Rian-Rasch/Projeto-I.-Eng.-El-trica---2024.1/Imagens Guia/Bateria Lítio.png

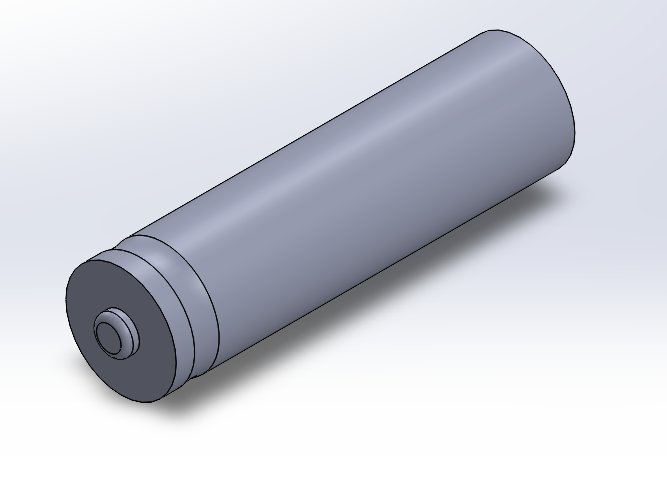
Imagens Guia/Bateria Lítio.png
