Rian-Rasch/Projeto-I.-Eng.-El-trica---2024.1/Imagens Guia/download.jpg

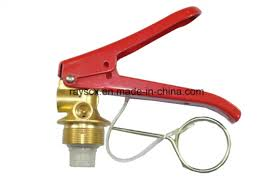
Imagens Guia/download.jpg
