Rian-Rasch/Projeto-I.-Eng.-El-trica---2024.1/Imagens Guia/EXTINTOR.png

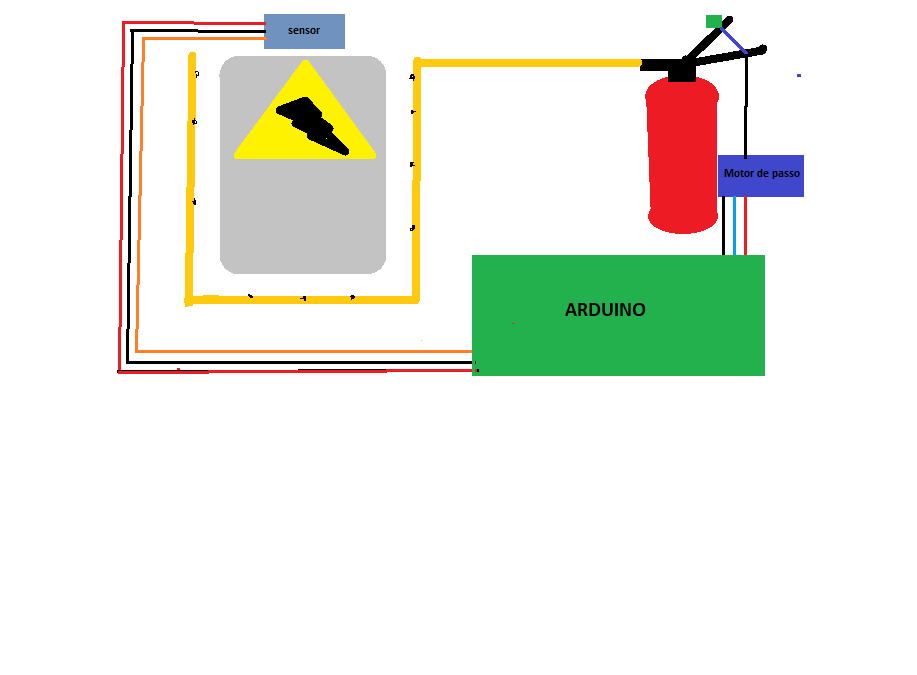
Imagens Guia/EXTINTOR.png
