Rian-Rasch/Projeto-I.-Eng.-El-trica---2024.1/Imagens Guia/S8efe8c3fdea14018a6a882b7f9c04156H.webp

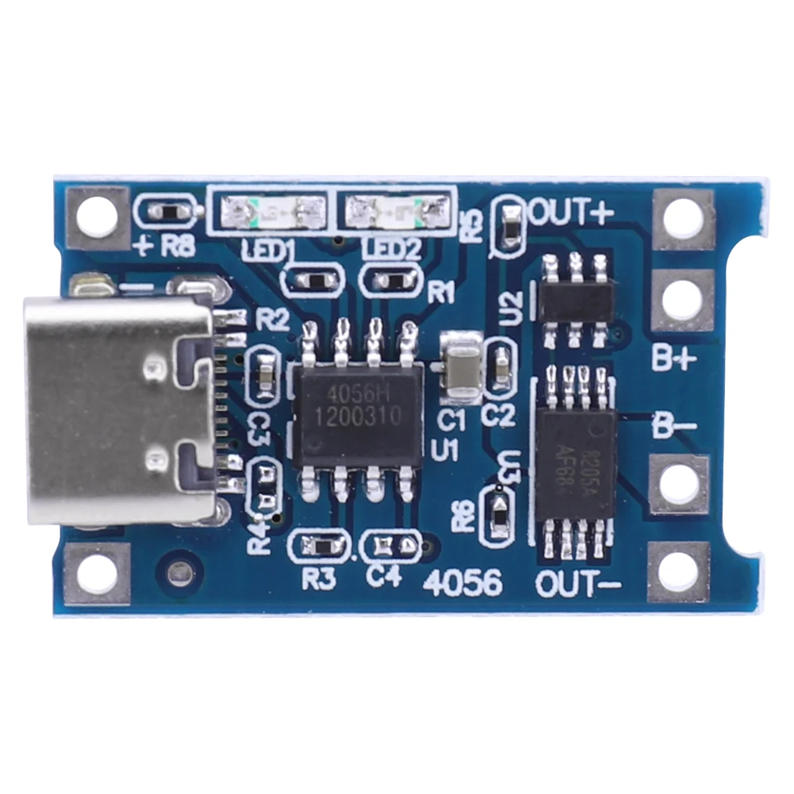
Imagens Guia/S8efe8c3fdea14018a6a882b7f9c04156H.webp
