Rian-Rasch/Projeto-I.-Eng.-El-trica---2024.1/Imagens Guia/Servomotor.png

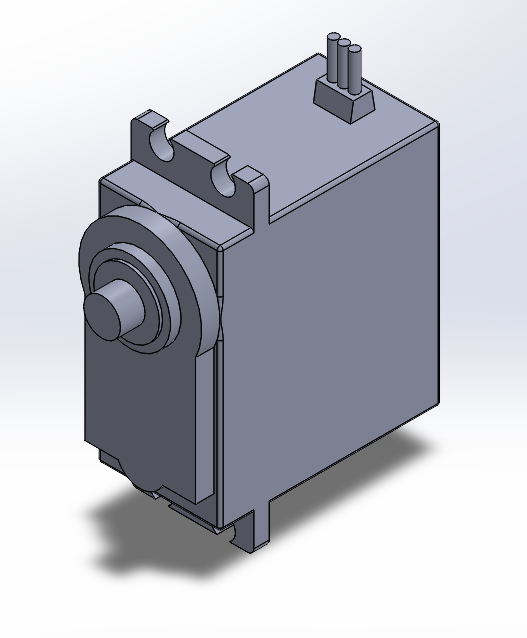
Imagens Guia/Servomotor.png
