Rian-Rasch/Projeto-I.-Eng.-El-trica---2024.1/Imagens Guia/Suporte Servo.png

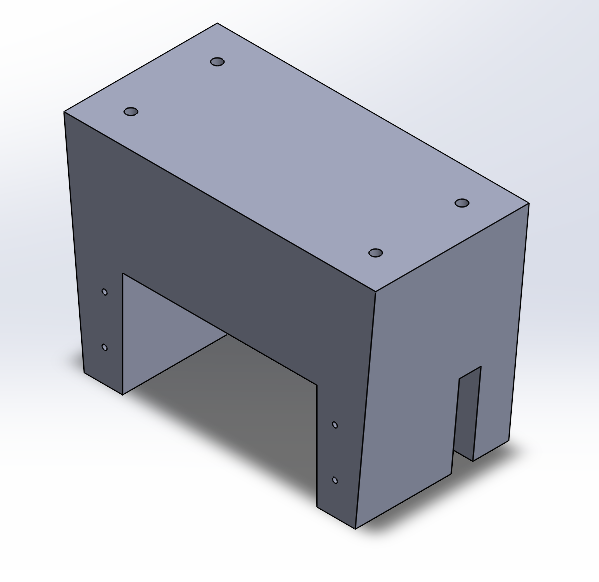
Imagens Guia/Suporte Servo.png
