Rian-Rasch/Projeto-I.-Eng.-El-trica---2024.1/Modelagens/envio para impressão/EXA200/Sentido de Impressão.PNG

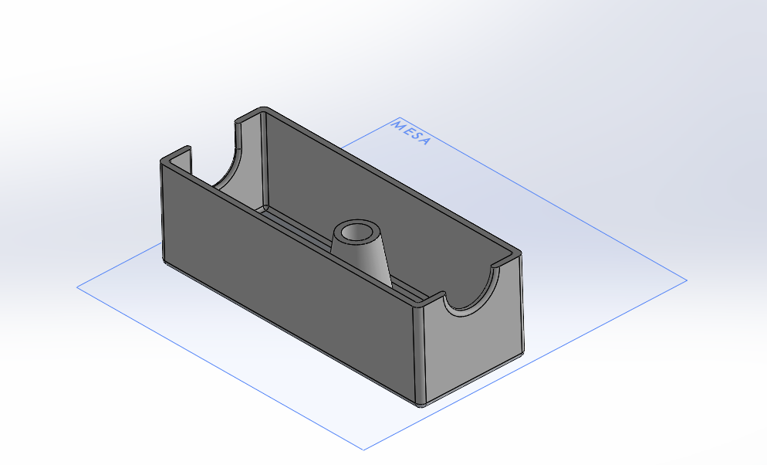
Modelagens/envio para impressão/EXA200/Sentido de Impressão.PNG
