Rian-Rasch/Projeto-I.-Eng.-El-trica---2024.1/Modelagens/envio para impressão/EXA230/Sentido da Impressão.PNG

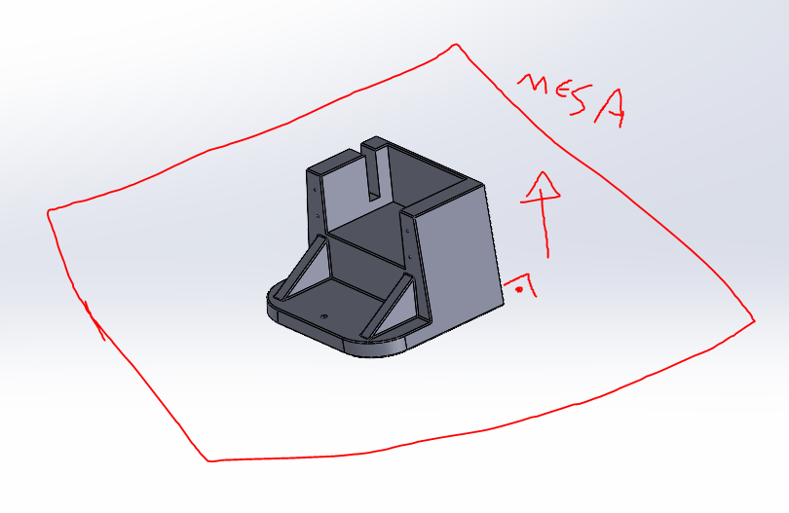
Modelagens/envio para impressão/EXA230/Sentido da Impressão.PNG
