Rian-Rasch/Projeto-I.-Eng.-El-trica---2024.1/Modelagens/envio para impressão/EXA231/Sentido da impressão.PNG

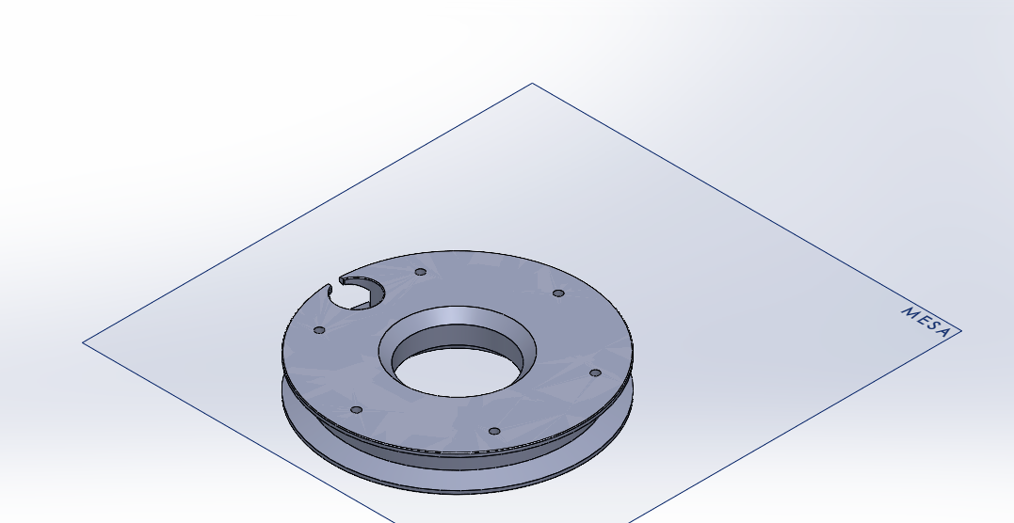
Modelagens/envio para impressão/EXA231/Sentido da impressão.PNG
