Rian-Rasch/Projeto-I.-Eng.-El-trica---2024.1/Modelagens/Marcus/abraçadeira.PNG

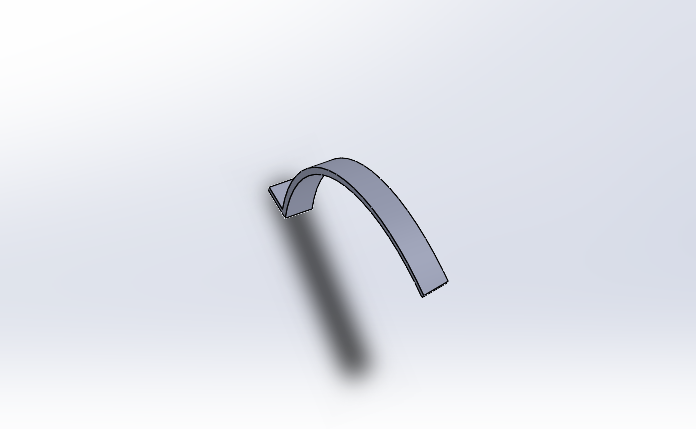
Modelagens/Marcus/abraçadeira.PNG
