Rian-Rasch/Projeto-I.-Eng.-El-trica---2024.1/Modelagens/Rian/9e9c7f35-f93e-415a-af5f-1c41aec8572a.jpg

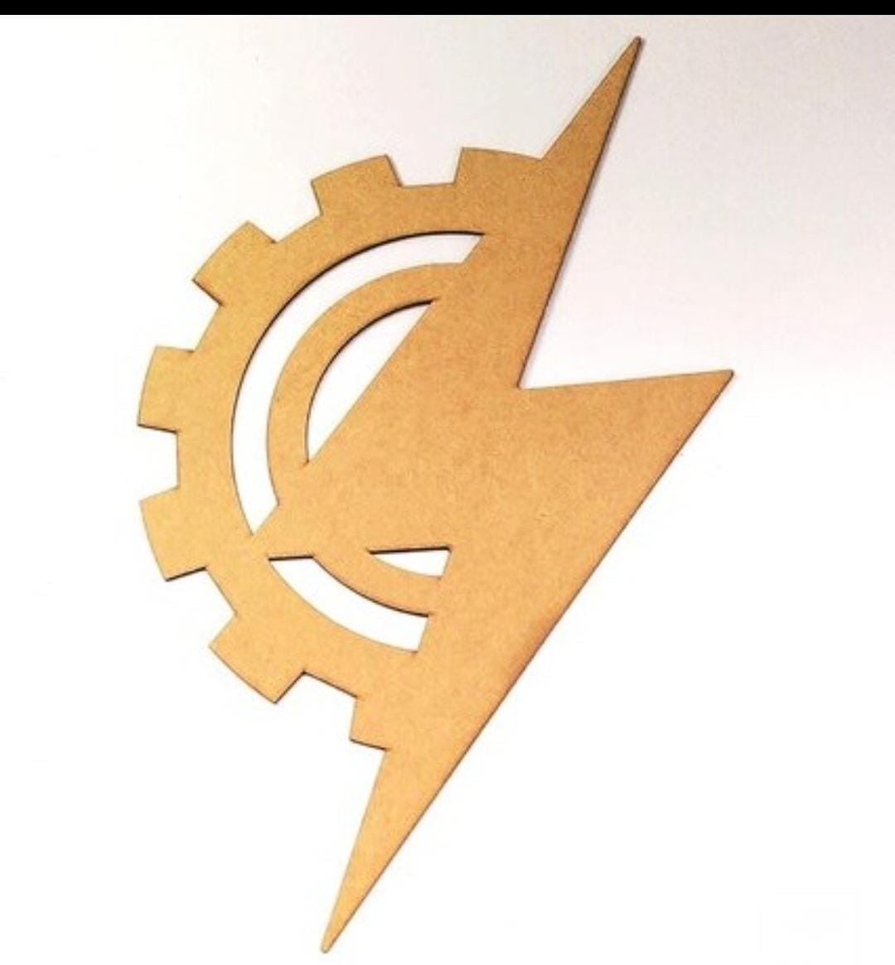
Modelagens/Rian/9e9c7f35-f93e-415a-af5f-1c41aec8572a.jpg
