Rian-Rasch/Projeto-I.-Eng.-El-trica---2024.1/Modelagens/Tonetto/Chaveiro Eng Eletrica.SLDPRT

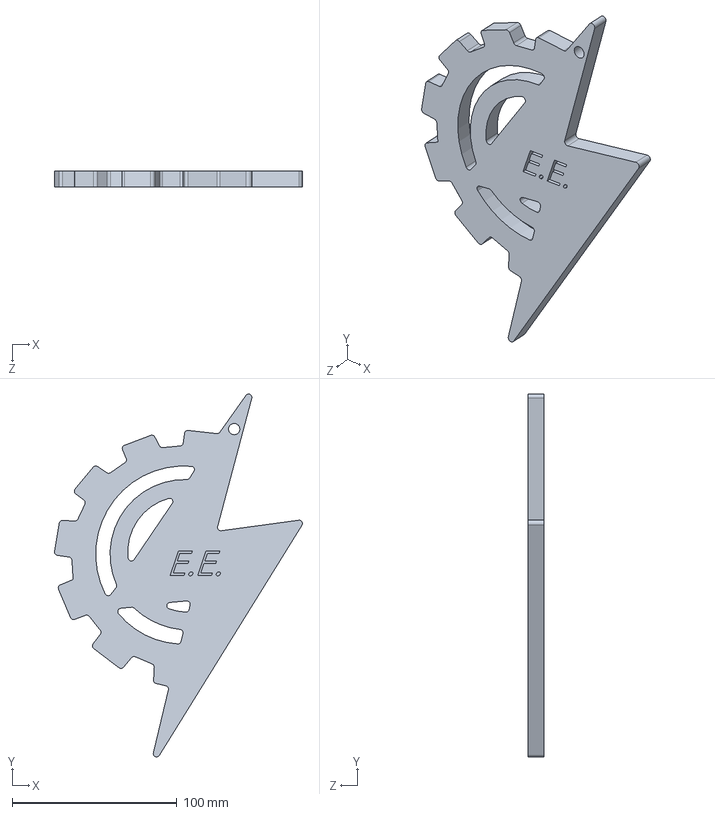
[picture p53: CAD file, 2024-06-25]
Modelagens/Tonetto/Chaveiro Eng Eletrica.SLDPRT
150.6 x 220.4 x 10.0 mm
