Rian-Rasch/Projeto-I.-Eng.-El-trica---2024.1/Modelagens/envio para impressão/dogtag2.STL

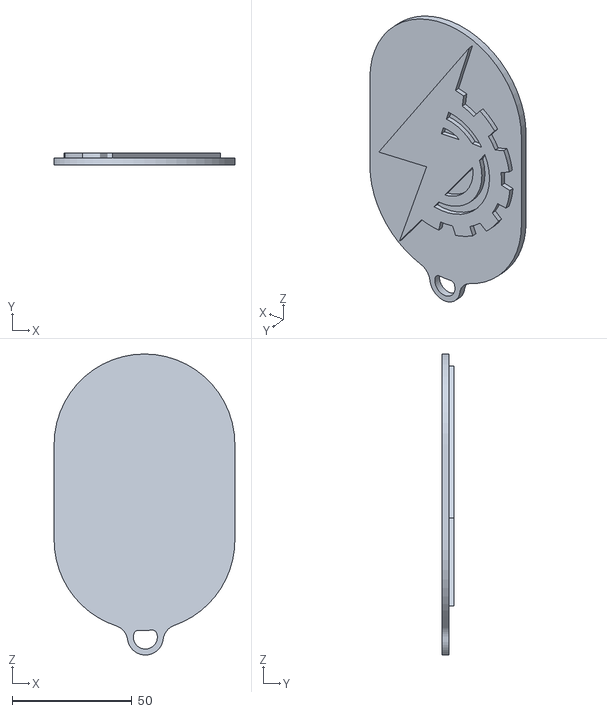
[picture p54: CAD file, 2024-06-30]
Modelagens/envio para impressão/dogtag2.STL
75.4 x 5.00 x 125.5
