Rian-Rasch/Projeto-I.-Eng.-El-trica---2024.1/Modelagens/Marcus/EXA_201.SLDPRT

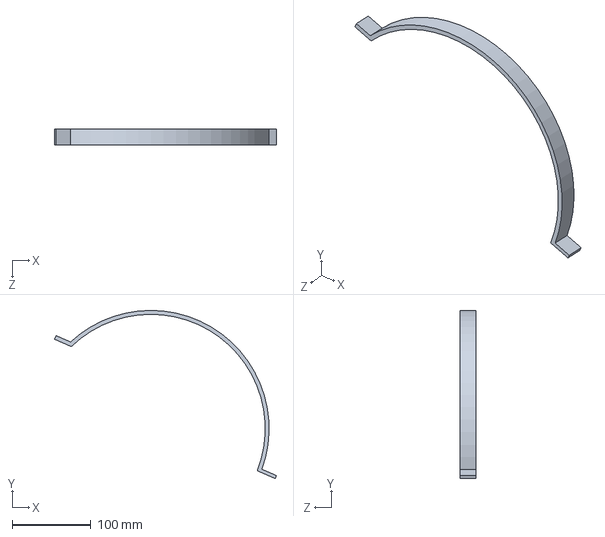
[picture p55: CAD file, 2024-06-03]
Modelagens/Marcus/EXA_201.SLDPRT
281.7 x 213.4 x 20.0 mm
