Rian-Rasch/Projeto-I.-Eng.-El-trica---2024.1/Modelagens/Tonetto/EXA222.SLDPRT

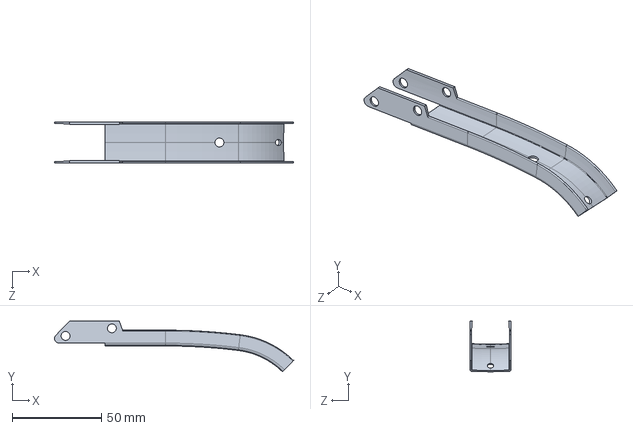
[picture p56: CAD file, 2024-06-17]
Modelagens/Tonetto/EXA222.SLDPRT
134.1 x 28.4 x 23.3 mm
