Rian-Rasch/Projeto-I.-Eng.-El-trica---2024.1/Modelagens/Marcus/Peça1.SLDPRT

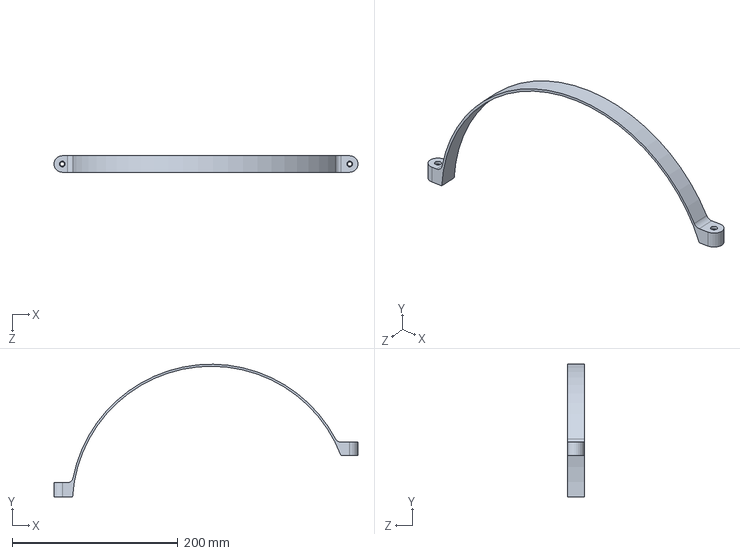
[picture p57: CAD file, 2024-06-03]
Modelagens/Marcus/Peça1.SLDPRT
366.8 x 160.0 x 20.0 mm
