Rian-Rasch/Projeto-I.-Eng.-El-trica---2024.1/Modelagens/envio para impressão/Logo 2mm.STL

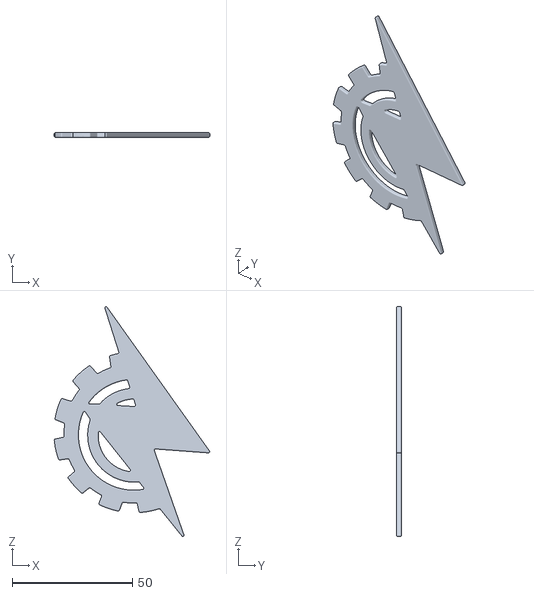
[picture p58: CAD file, 2024-06-30]
Modelagens/envio para impressão/Logo 2mm.STL
64.6 x 2.00 x 95.5
