Rian-Rasch/Projeto-I.-Eng.-El-trica---2024.1/Modelagens/Tonetto/Cabo de aço.SLDPRT

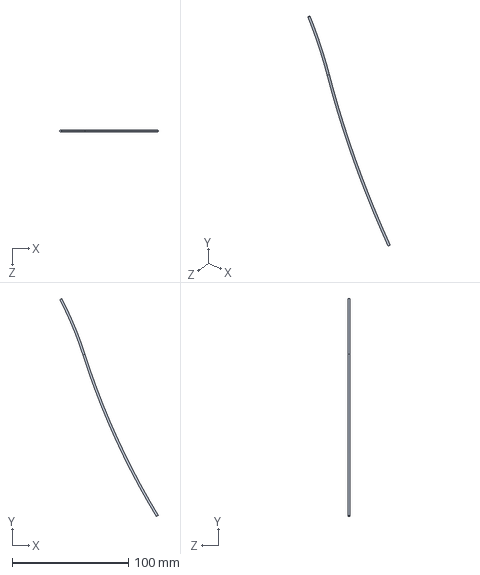
[picture p59: CAD file, 2024-06-17]
Modelagens/Tonetto/Cabo de aço.SLDPRT
84.8 x 187.4 x 2.00 mm
