Rian-Rasch/Projeto-I.-Eng.-El-trica---2024.1/Modelagens/Rian/EXA131.SLDPRT

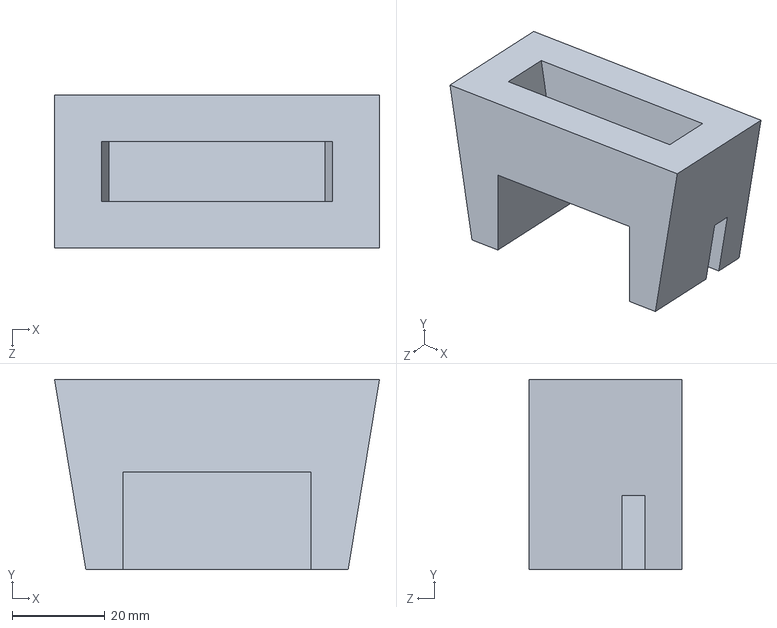
[picture p60: CAD file, 2024-06-13]
Modelagens/Rian/EXA131.SLDPRT
70.0 x 41.0 x 33.0 mm
