Rian-Rasch/Projeto-I.-Eng.-El-trica---2024.1/Modelagens/Tonetto/EXA212.SLDPRT

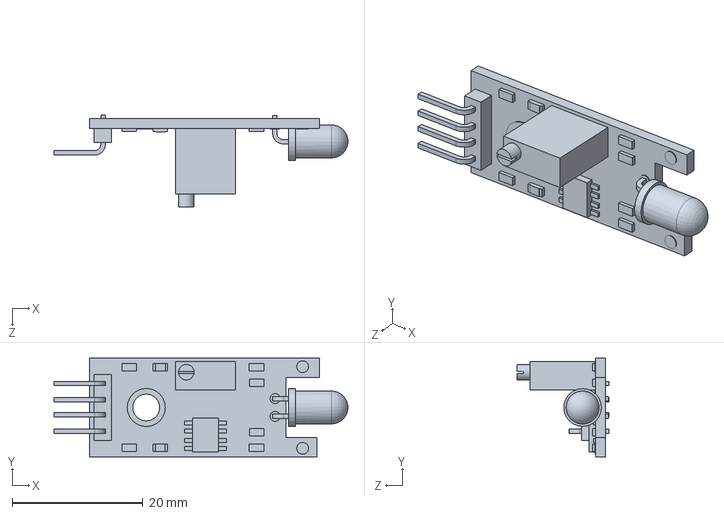
[picture p61: CAD file, 2024-06-17]
Modelagens/Tonetto/EXA212.SLDPRT
44.9 x 15.1 x 14.0 mm
