Rian-Rasch/Projeto-I.-Eng.-El-trica---2024.1/Modelagens/Rian/EXA130.SLDPRT

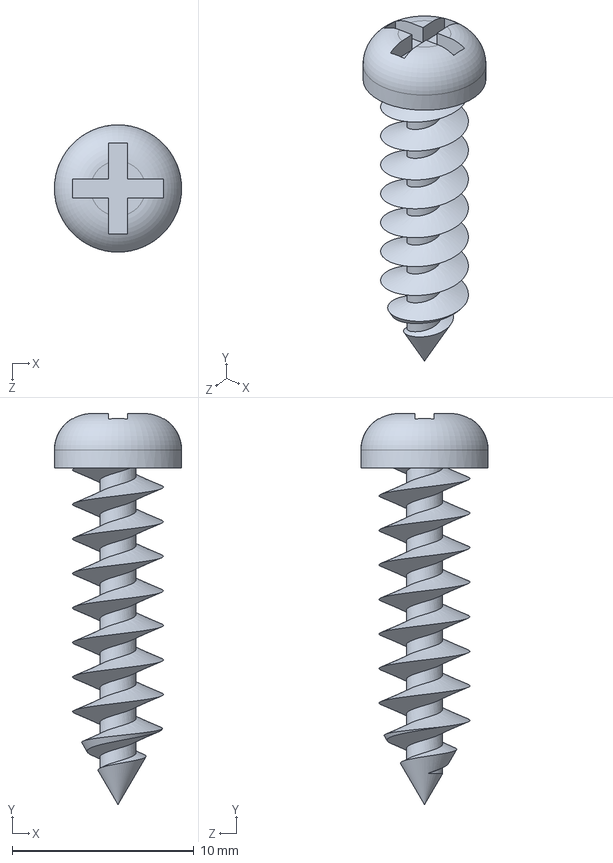
[picture p62: CAD file, 2024-06-09]
Modelagens/Rian/EXA130.SLDPRT
7.00 x 21.5 x 7.00 mm
