Rian-Rasch/Projeto-I.-Eng.-El-trica---2024.1/Modelagens/Tonetto/EXA213.SLDPRT

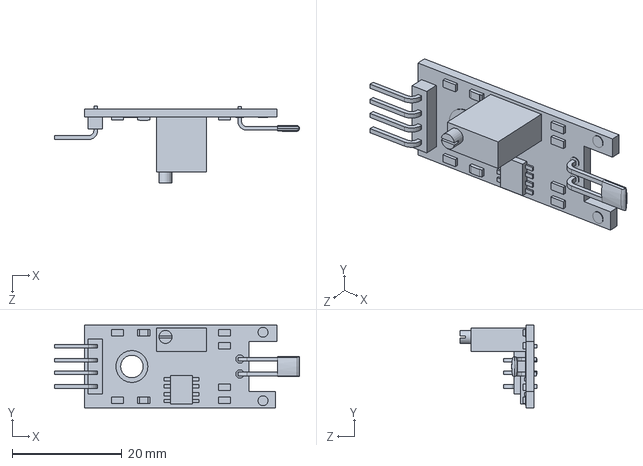
[picture p63: CAD file, 2024-06-17]
Modelagens/Tonetto/EXA213.SLDPRT
44.6 x 15.1 x 14.0 mm
