Rian-Rasch/Projeto-I.-Eng.-El-trica---2024.1/Modelagens/Rian/EXA115.SLDPRT

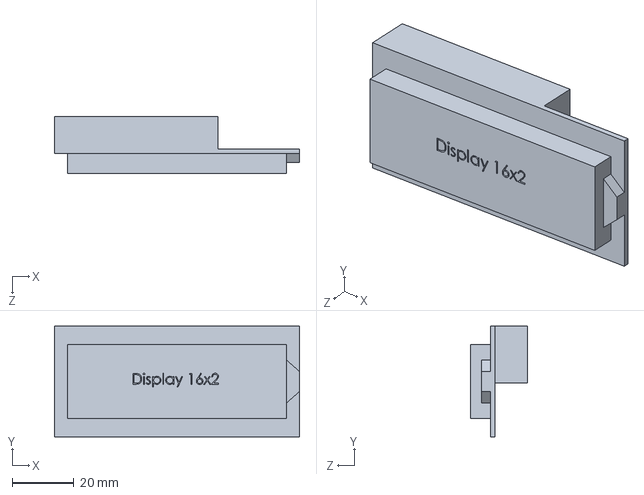
[picture p64: CAD file, 2024-06-07]
Modelagens/Rian/EXA115.SLDPRT
79.5 x 36.0 x 18.5 mm
