Rian-Rasch/Projeto-I.-Eng.-El-trica---2024.1/Modelagens/Rian/EXA121.SLDPRT

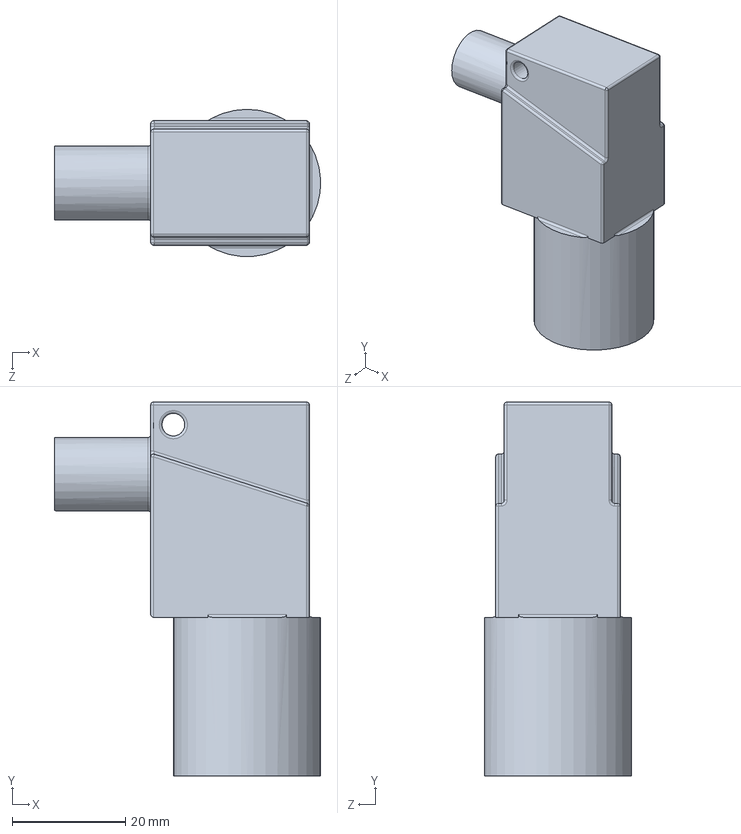
[picture p65: CAD file, 2024-06-03]
Modelagens/Rian/EXA121.SLDPRT
47.0 x 66.0 x 26.0 mm
