Rian-Rasch/Projeto-I.-Eng.-El-trica---2024.1/Modelagens/Rian/EXA120.SLDPRT

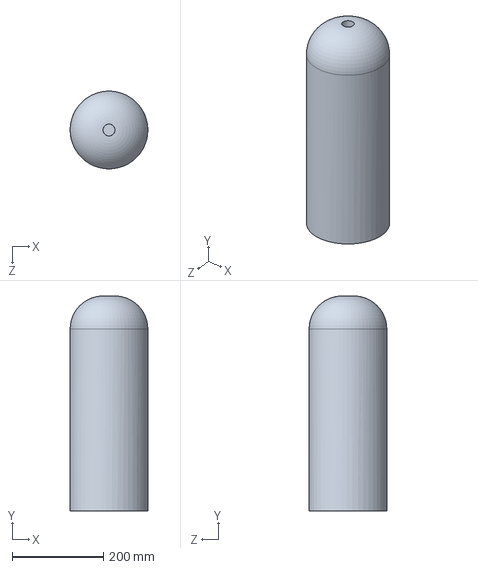
[picture p66: CAD file, 2024-06-03]
Modelagens/Rian/EXA120.SLDPRT
169.9 x 470.0 x 170.0 mm
