Rian-Rasch/Projeto-I.-Eng.-El-trica---2024.1/Modelagens/Tonetto/EXA232.SLDPRT

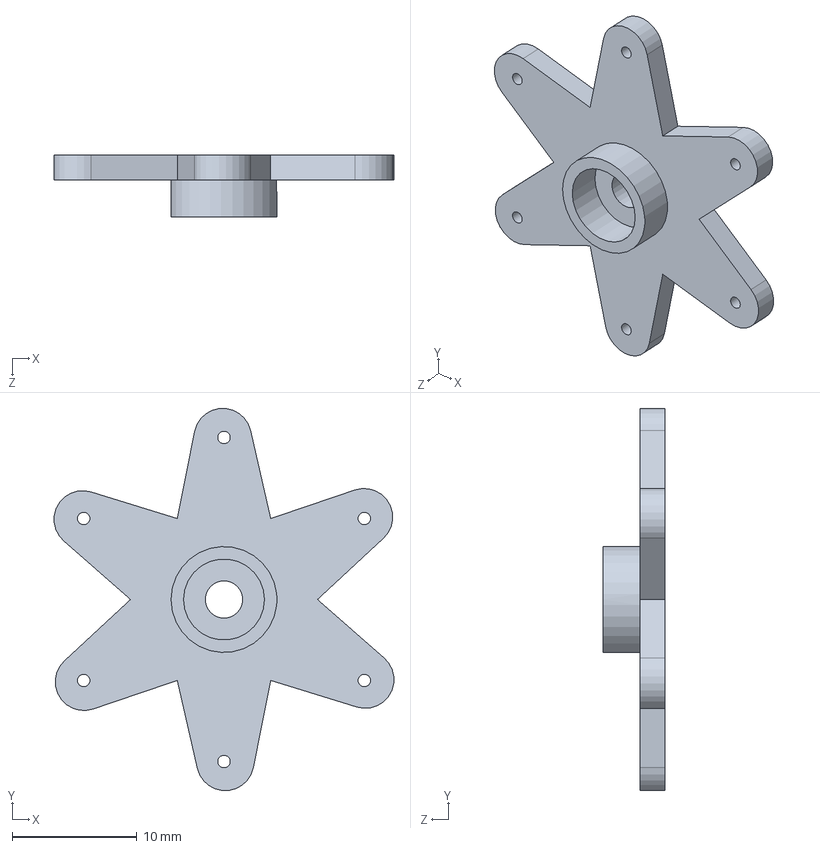
[picture p67: CAD file, 2024-06-13]
Modelagens/Tonetto/EXA232.SLDPRT
27.3 x 30.7 x 5.00 mm
