Rian-Rasch/Projeto-I.-Eng.-El-trica---2024.1/Modelagens/Tonetto/EXA211.SLDPRT

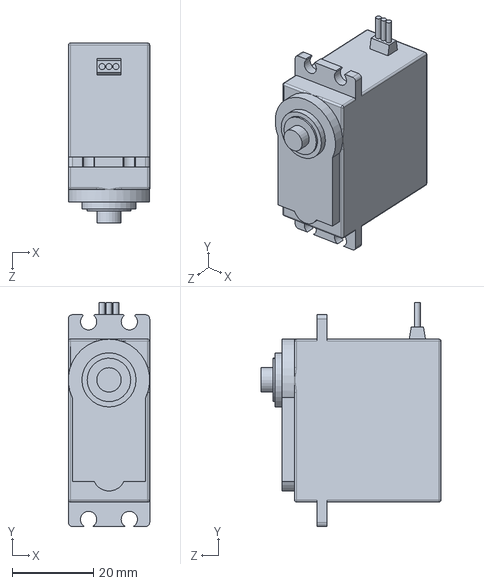
[picture p68: CAD file, 2024-06-13]
Modelagens/Tonetto/EXA211.SLDPRT
20.0 x 55.0 x 44.2 mm
