Rian-Rasch/Projeto-I.-Eng.-El-trica---2024.1/Modelagens/Tonetto/EXA223.SLDPRT

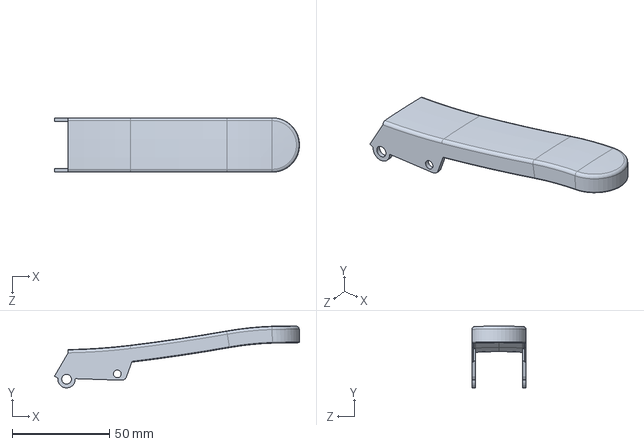
[picture p69: CAD file, 2024-06-09]
Modelagens/Tonetto/EXA223.SLDPRT
125.9 x 31.8 x 28.0 mm
