Rian-Rasch/Projeto-I.-Eng.-El-trica---2024.1/Modelagens/Tonetto/EXA210.SLDPRT

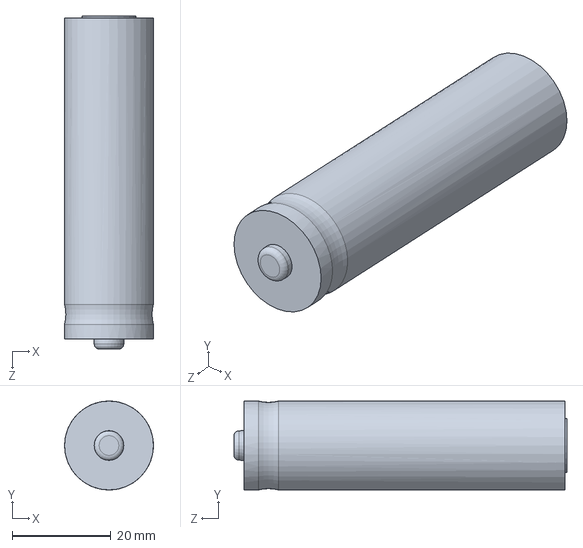
[picture p70: CAD file, 2024-06-07]
Modelagens/Tonetto/EXA210.SLDPRT
18.0 x 18.0 x 67.4 mm
