Rian-Rasch/Projeto-I.-Eng.-El-trica---2024.1/Modelagens/Tonetto/EXA310.SLDPRT

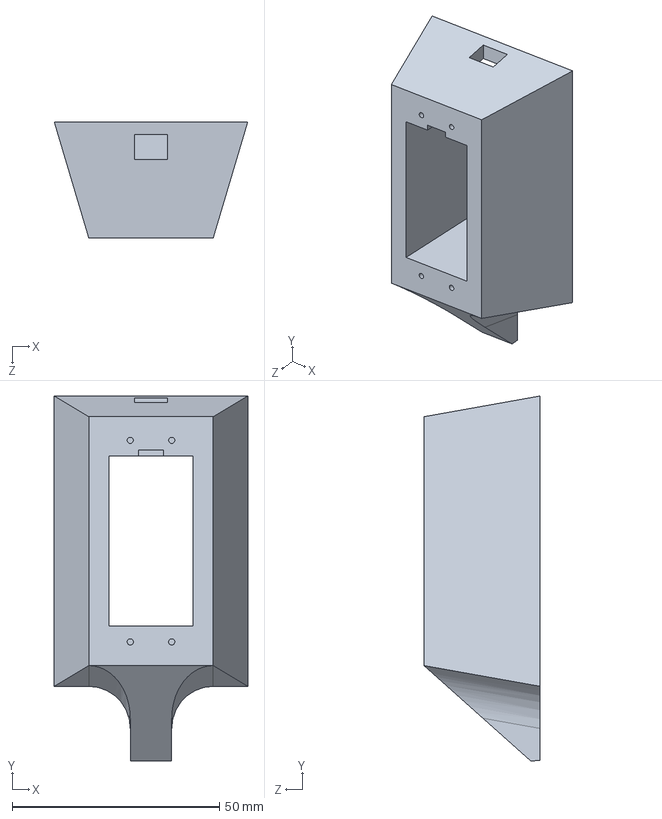
[picture p71: CAD file, 2024-06-04]
Modelagens/Tonetto/EXA310.SLDPRT
46.7 x 88.0 x 28.0 mm
