Rian-Rasch/Projeto-I.-Eng.-El-trica---2024.1/Imagens Guia/montagem com valvula3.PNG

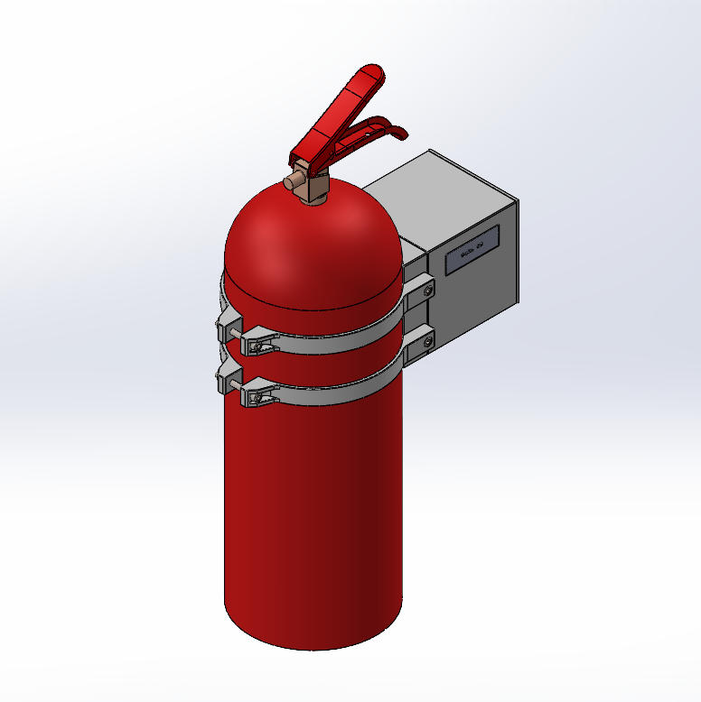
Imagens Guia/montagem com valvula3.PNG
