Rian-Rasch/Projeto-I.-Eng.-El-trica---2024.1/Imagens Guia/Montagem Motor, suporte, polia.png

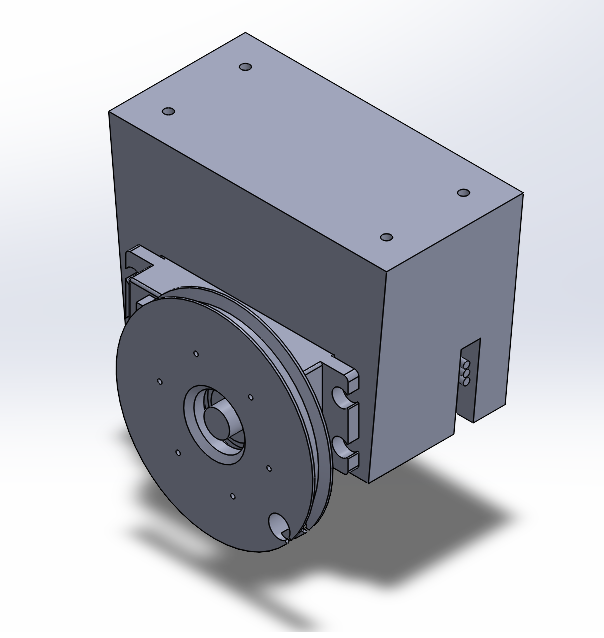
Imagens Guia/Montagem Motor, suporte, polia.png
