Rian-Rasch/Projeto-I.-Eng.-El-trica---2024.1/Imagens Guia/Montagem Servo com Suporte.png

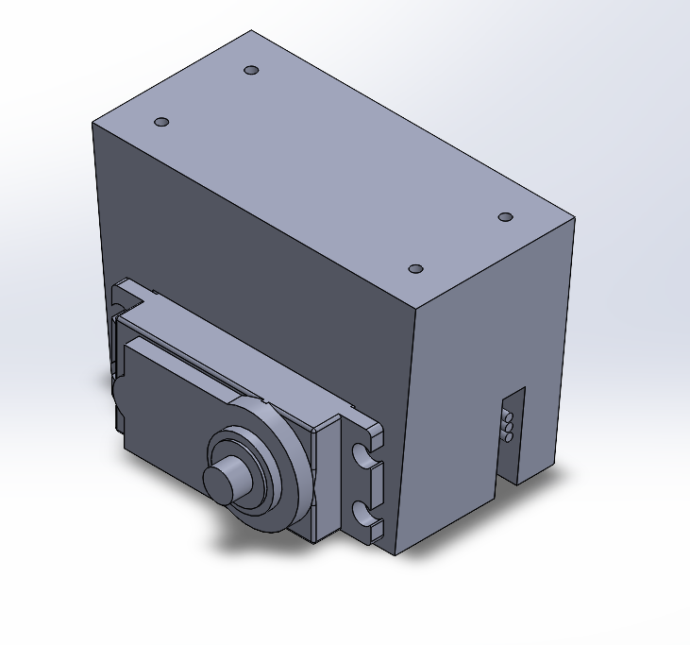
Imagens Guia/Montagem Servo com Suporte.png
