Rian-Rasch/Projeto-I.-Eng.-El-trica---2024.1/Modelagens/Desenhos/EXA301.pdf

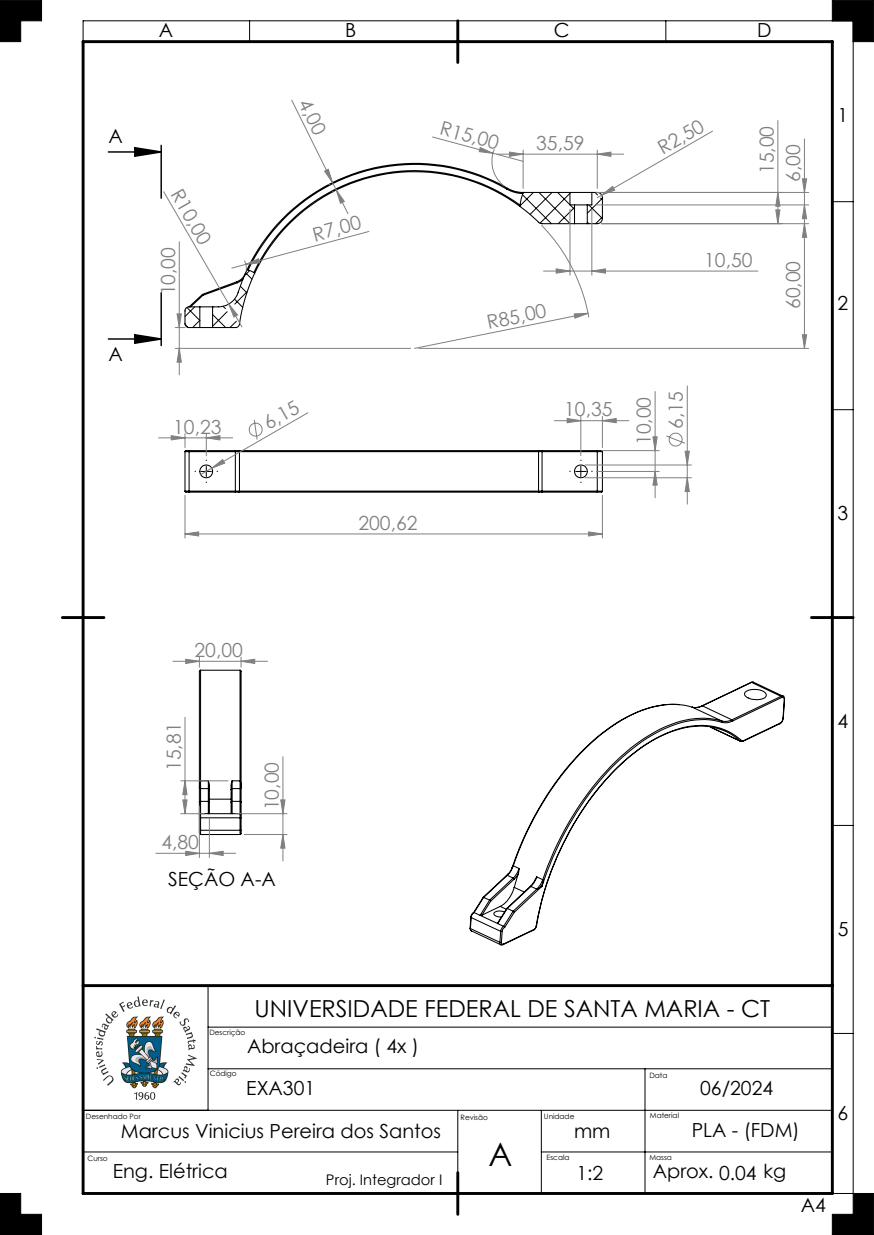
[picture p84: page 1]
SEÇÃO A-A

UNIVERSIDADE FEDERAL DE SANTA MARIA - CT
Abraçadeira ( 4x )

Código EXA301 | Data 06/2024

Desenhado Por Marcus Vinicius Pereira dos Santos | Revisão A | Unidade mm | Material PLA - (FDM)

Curso Eng. Elétrica Proj. Integrador I | | Escala 1:2 | Massa Aprox. 0.04 kg
